sperlingn/PiSmoker/TemperatureProbe.py

from math import sqrt, exp
from functools import partial

# Constants for temperature probe type
THERMOCOUPLE = 'TC'
THERMISTOR = 'TR'
RTD = 'RTD'
VALID_PROBE_TYPES = [RTD, THERMISTOR, THERMOCOUPLE]

# Parameters for RTD correction from IEC 751 (PT100)
# Solved for alpha = 0.00385055
# RTD Constants
_A_PT = 3.90830e-3
_B_PT = -5.775e-7
_R_0_PT100 = 100.
_R_0_PT1000 = 1000.


class Thermocouple(object):
    c2e_ranges = {
        'B': [630.615, 1820.000],
        'E': [0.000, 1000.000],
        'J': [760.000, 1200.000],
        'K': [0.000, 1372.000],
        'N': [0.000, 1300.],
        'R': [1064.180, 1664.500, 1768.1],
        'S': [1064.180, 1664.500, 1768.1],
        'T': [0.000, 400.000]
    }
    c2e_coefs = {
        'B': [[0.000000000000E+00, -0.246508183460E-03, 0.590404211710E-05, -0.132579316360E-08, 0.156682919010E-11,
               -0.169445292400E-14, 0.629903470940E-18],
              [-0.389381686210E+01, 0.285717474700E-01, -0.848851047850E-04, 0.157852801640E-06, -0.168353448640E-09,
               0.111097940130E-12, -0.445154310330E-16, 0.989756408210E-20, -0.937913302890E-24]],
        'E': [[0.000000000000E+00, 0.586655087080E-01, 0.454109771240E-04, -0.779980486860E-06, -0.258001608430E-07,
               -0.594525830570E-09, -0.932140586670E-11, -0.102876055340E-12, -0.803701236210E-15, -0.439794973910E-17,
               -0.164147763550E-19, -0.396736195160E-22, -0.558273287210E-25, -0.346578420130E-28],
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
               0.000000000E+00, 0.000000000E+00, 0.000000000E+00, 0.000000000E+00],
              [5.333875126E+04, -1.235892298E+04, 1.092657613E+03, -4.265693686E+01, 6.247205420E-01, 0.000000000E+00,
               0.000000000E+00, 0.000000000E+00, 0.000000000E+00, 0.000000000E+00]],
        'T': [[0.0000000E+00, 2.5949192E+01, -2.1316967E-01, 7.9018692E-01, 4.2527777E-01, 1.3304473E-01, 2.0241446E-02,
               1.2668171E-03],
              [0.000000E+00, 2.592800E+01, -7.602961E-01, 4.637791E-02, -2.165394E-03, 6.048144E-05, -7.293422E-07,
               0.000000E+00]]
    }

    def __init__(self, tc_type='K'):
        if tc_type not in self.c2e_ranges.keys():
            raise TypeError("Thermocouple type '%s' invalid." % tc_type)

        self.type = tc_type

    def c2e(self, Tc):
        """Converts temperature in C to equivalent thermocouple voltage in Volts using NIST ITS-90 functions.

        @param Tc: Temperature (C)
        @type Tc: float
        @return: Voltage (Volts)
        @rtype: float
        """
        E = 0
        # Gets index for coefs for which the NIST function is valid
        t_r = 0
        while t_r < len(self.c2e_ranges[self.type]) - 1 and self.c2e_ranges[self.type][t_r] <= Tc:
            t_r += 1

        # Recursive formulation of polynomial coefficient solution.
        for a in range(len(self.c2e_coefs[self.type][t_r]) - 1, -1, -1):
            E = self.c2e_coefs[self.type][t_r][a] + Tc * E

        if self.type is 'K':
            # Special K-type corrections.
            E += 0.1185976 * exp(-0.1183432e-3 * (Tc - 0.1269686e3) ** 2)

        return E / 1000.  # Units of NIST ITS-90 are mV

    def e2c(self, E):
        """Convert reading in V to reading in C for Thermocouple type using NIST ITS-90 functions.

        @param E: Reading (V)
        @type E: float
        @return: Temperature (C)
        @rtype: float
        """
        Tc = 0.

        E_mV = E * 1000.  # NIST ITS-90 data all computed in mV

        # Gets index for coefs for which the NIST function is valid
        e_r = 0
        while e_r < len(self.e2c_ranges[self.type]) - 1 and self.e2c_ranges[self.type][e_r] <= E_mV:
            e_r += 1

        # Recursive formulation of polynomial coefficient solution.
        for a in range(len(self.e2c_coefs[self.type][e_r]) - 1, -1, -1):
            Tc = self.e2c_coefs[self.type][e_r][a] + E_mV * Tc

        return Tc


# noinspection SpellCheckingInspection
class TemperatureProbe(object):
    # TODO: Sliding window temperature log.
    # As a new temperature is added, remove the last one in the window. FIFO queue?
    temp_in_F = False
    type = None

    tc_type = 'K'
    tc_probe = None  # @type tc_probe: Thermocouple

    # User functions to read various required parameters.
    #  Thermistors require thermis_fn, thermocouples require read_cj_fn, all require read_fn
    read_fn = None  # Function used to read voltage from ADC
    read_cj_fn = None  # Function used to read Cold Junction temperature for thermocouple
    thermis_fn = None  # Arbitrary voltage to temperature function for thermistors

    R_0_RTD = _R_0_PT1000

    def __init__(self, probe_type, read_fn, read_fn_args=None, read_cj_fn=None, read_cj_fn_args=None, subtype=None,
                 thermis_fn=None, thermis_fn_args=None, temp_in_F=None, **kwargs):
        """

        @param probe_type: Probe type, recognizes: [RTD, THERMISTOR, THERMOCOUPLE] (['RTD', 'TR', 'TC'])
        @type probe_type:  str
        @param read_fn:  Function which returns the ADC voltage. Signature read_fn(*read_fn_args,**read_fn_kwargs)
        @type read_fn: callable
        @param read_fn_args: Positional parameters for read_fn
        @type read_fn_args: tuple
        @param read_cj_fn: Function to obtain the cold junction temperature. Signature read_cj_fn(*read_cj_fn_args,...)
        @type read_cj_fn: callable
        @param read_cj_fn_args: Positional parameters for read_cj_fn
        @type read_cj_fn_args: tuple
        @param subtype: Sensor subtype: e.g. 'K' for Thermocouple, 'PT100' for RTD, etc. (default: 'K', 'PT100', None)
        @type subtype: str
        @param thermis_fn: Function for thermistor voltage to temperature. Signature thermis_fn(V,*thermis_fn_args,...)
        @type thermis_fn:  callable
        @param thermis_fn_args:  Positional parameters for pos>1,
        @type thermis_fn_args: tuple
        @param *_fn_kwargs: Keyword arguments set for any of the callable functions, will be passed directly.
        @type *_fn_kwargs: dict
        """

        if probe_type not in VALID_PROBE_TYPES:
            raise TypeError("Invalid probe type: %s" % probe_type)

        if probe_type is THERMOCOUPLE:
            if read_cj_fn is None or not callable(read_cj_fn):
                raise TypeError("Probe type Thermocouple requires a callable read_cj_fn")

            self.read_cj_fn = read_cj_fn
            if 'read_cj_fn_kwargs' in kwargs:
                self.read_cj_fn = partial(self.read_cj_fn, **kwargs['read_cj_fn_kwargs'])
            if read_cj_fn_args is not None:
                try:
                    self.read_cj_fn = partial(self.read_cj_fn, *read_cj_fn_args)
                except TypeError:
                    self.read_cj_fn = partial(self.read_cj_fn, read_cj_fn_args)
            if subtype is not None:
                self.tc_type = subtype
            self.tc_probe = Thermocouple(self.tc_type)
        elif probe_type is THERMISTOR:
            if thermis_fn is None or not callable(thermis_fn):
                raise TypeError("Probe type Thermistor requires a callable thermis_fn")

            self.thermis_fn = thermis_fn
            if 'thermis_fn_kwargs' in kwargs:
                self.thermis_fn = partial(self.thermis_fn, **kwargs['thermis_fn_kwargs'])
            if thermis_fn_args is not None:
                try:
                    self.thermis_fn = partial(self.thermis_fn, *thermis_fn_args)
                except TypeError:
                    self.thermis_fn = partial(self.thermis_fn, thermis_fn_args)
        elif probe_type is RTD and subtype is not None:
            if subtype == 'PT100':
                self.R_0_RTD = _R_0_PT100
            elif subtype == 'PT1000':
                self.R_0_RTD = _R_0_PT1000
            else:
                self.R_0_RTD = float(subtype)

        if not callable(read_fn):
            assert callable(read_fn)
            raise TypeError("read_fn must be a callable object")
        else:
            self.read_fn = read_fn
            if 'read_fn_kwargs' in kwargs:
                self.read_fn = partial(self.read_fn, **kwargs['read_fn_kwargs'])
            if read_fn_args is not None:
                try:
                    self.read_fn = partial(self.read_fn, *read_fn_args)
                except TypeError:
                    self.read_fn = partial(self.read_fn, read_fn_args)

        self.type = probe_type

        if temp_in_F is not None:
            self.temp_in_F = temp_in_F

    def _read_RTD(self):
        return self.rtd_conversion(self.read_fn())

    def _read_THERMOCOUPLE(self):

        # Measure cold junction temperature, and convert to voltage for this thermocouple.
        cjv = self.tc_probe.c2e(self.read_cj_fn())

        # Temperature for probe calculated from CJV + Voltage.
        return self.tc_probe.e2c(self.read_fn() + cjv)

    def _read_THERMISTOR(self):
        raise NotImplementedError("Thermistor reading not implemented in this class.")
        pass

    def rtd_conversion(self, R_T):
        # Use NIST RTD Linearization function.
        Tc = (-_A_PT + sqrt(_A_PT * _A_PT - 4 * _B_PT * (1 - R_T / self.R_0_RTD))) / (2 * _B_PT)
        return Tc

    def read(self, temp_in_F=None):
        """Read voltage using read_fn and convert to a temperature in default unit

        @param temp_in_F: Return temperature in degrees Fahrenheit? (False for deg. Celsius). Overrides default.
        @type temp_in_F: bool
        @return: Temperature read by probe.
        @rtype: float
        """
        if self.type == RTD:
            Tc = self._read_RTD()
        elif self.type == THERMOCOUPLE:
            Tc = self._read_THERMOCOUPLE()
        elif self.type == THERMISTOR:
            Tc = self._read_THERMISTOR()
        else:
            raise TypeError("Unknown probe type %s" % self.type)

        if temp_in_F is None:
            temp_in_F = self.temp_in_F

        if temp_in_F:
            T = Tc * 9 / 5 + 32
        else:
            T = Tc

        return T
